glued2/food-caddy-stl/production/food_caddy_k1se_liner_hanger_plate.stl

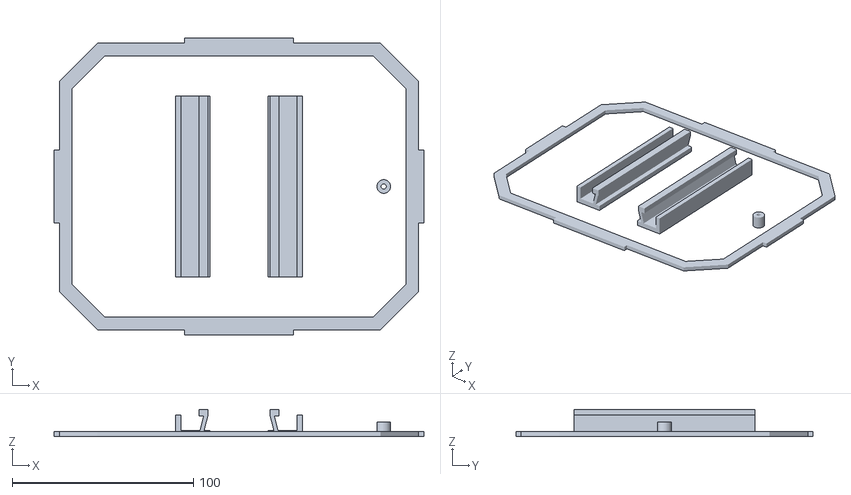
[picture p15: CAD file, 2026-09-11]
production/food_caddy_k1se_liner_hanger_plate.stl
204.0 x 164.0 x 15.0
