glued2/food-caddy-stl/spares/r4-coupon-rear-joint.stl

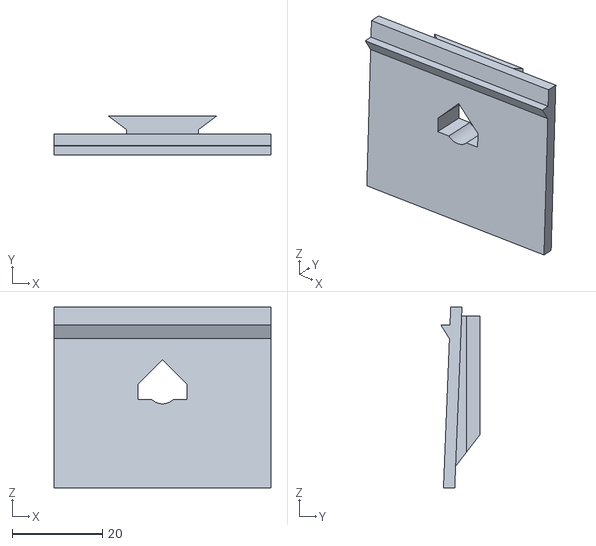
[picture p16: CAD file, 2026-09-12]
spares/r4-coupon-rear-joint.stl
48.0 x 8.66 x 40.0
