glued2/food-caddy-stl/spares/r4-coupon-gauge-keeper.stl

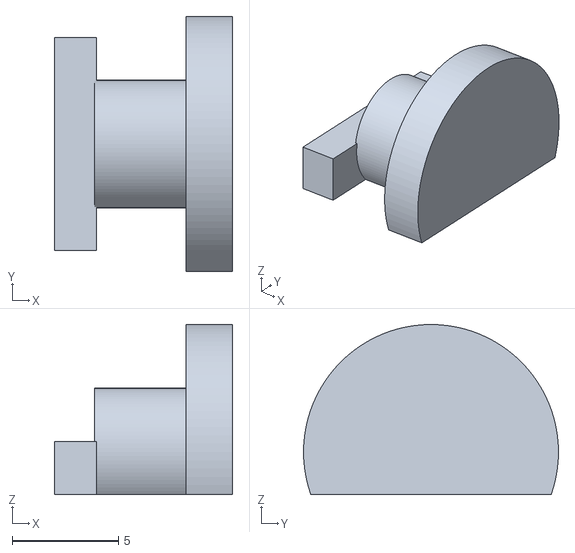
[picture p17: CAD file, 2026-09-12]
spares/r4-coupon-gauge-keeper.stl
8.40 x 12.0 x 8.00
