glued2/food-caddy-stl/production/food_caddy_k1se_failed_parts_only.stl

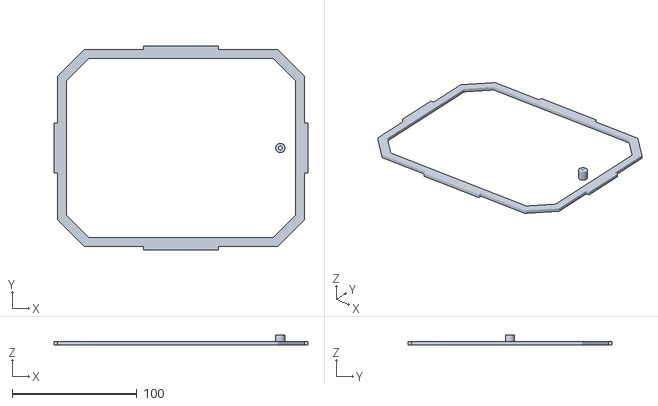
[picture p18: CAD file, 2026-09-11]
production/food_caddy_k1se_failed_parts_only.stl
204.0 x 164.0 x 8.00
