glued2/food-caddy-stl/spares/r4-coupon-corner.stl

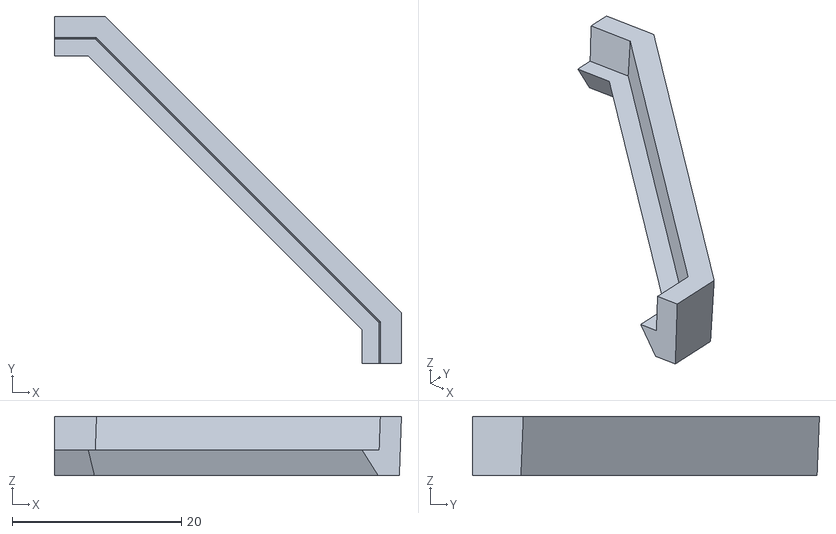
[picture p19: CAD file, 2026-09-12]
spares/r4-coupon-corner.stl
41.0 x 41.0 x 7.00
