glued2/food-caddy-stl/production/food_caddy_k1se_accessories_everything_bed_centered.stl

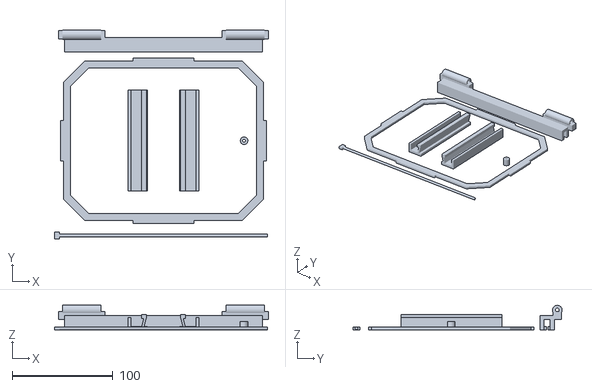
[picture p20: CAD file, 2026-09-11]
production/food_caddy_k1se_accessories_everything_bed_centered.stl
212.0 x 207.3 x 24.3
