glued2/food-caddy-stl/spares/r4-coupon-host-right.stl

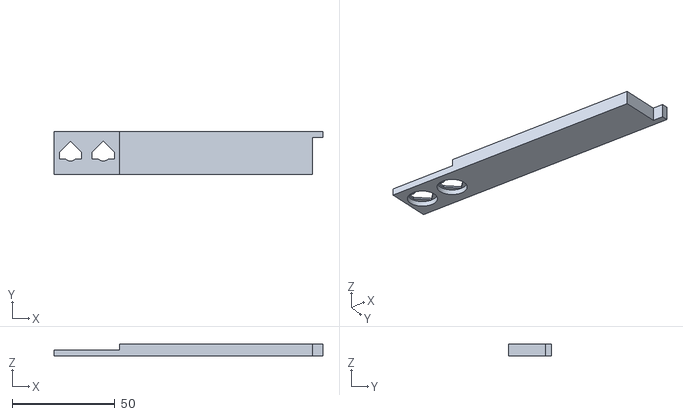
[picture p21: CAD file, 2026-09-12]
spares/r4-coupon-host-right.stl
131.0 x 21.0 x 6.00
