glued2/food-caddy-stl/spares/r4-coupon-axle-bores.stl

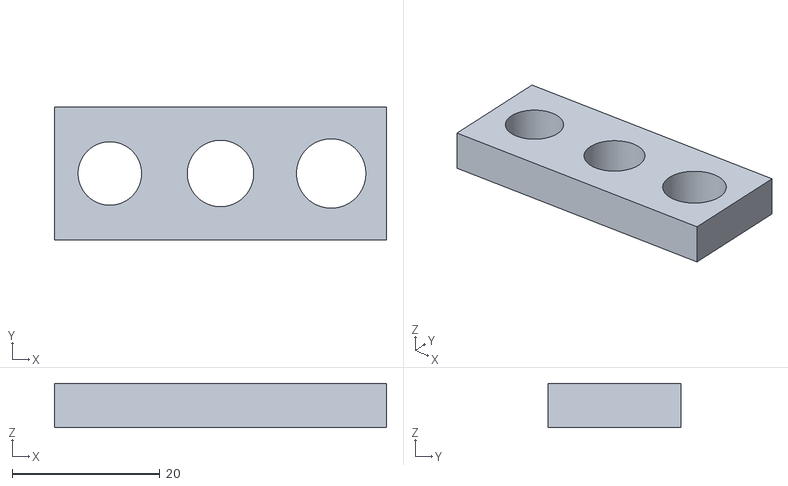
[picture p22: CAD file, 2026-09-12]
spares/r4-coupon-axle-bores.stl
45.0 x 18.0 x 6.00
