glued2/food-caddy-stl/spares/r4-coupon-lid-joint.stl

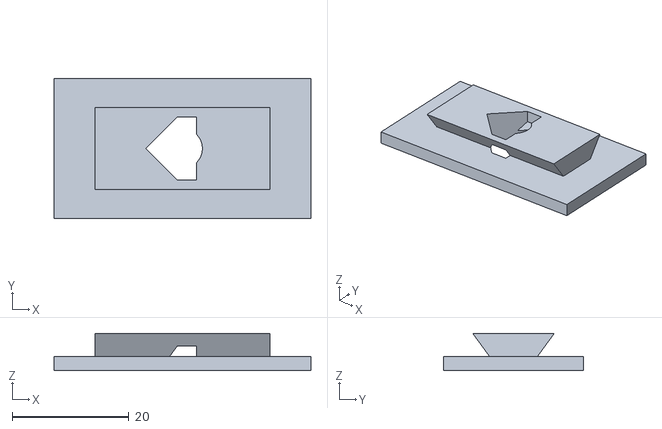
[picture p23: CAD file, 2026-09-12]
spares/r4-coupon-lid-joint.stl
44.0 x 24.0 x 6.40
