glued2/food-caddy-stl/production/food_caddy_k1se_hinge_kit_plate_bed_centered.stl

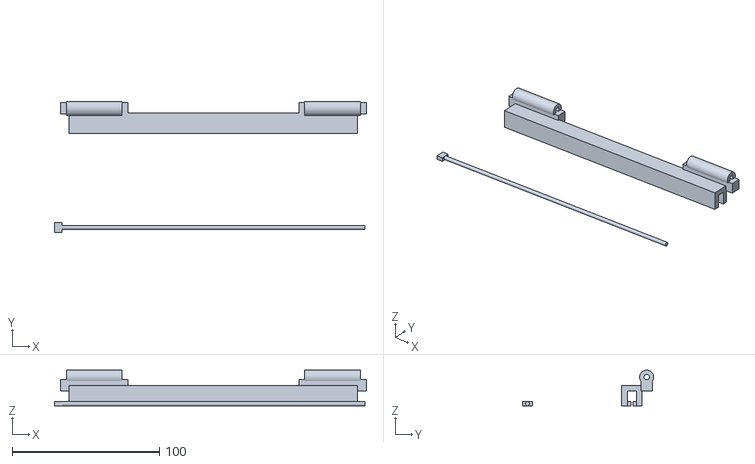
[picture p24: CAD file, 2026-09-07]
production/food_caddy_k1se_hinge_kit_plate_bed_centered.stl
212.0 x 89.3 x 24.3
