glued2/food-caddy-stl/spares/r4-hinge-rail.stl

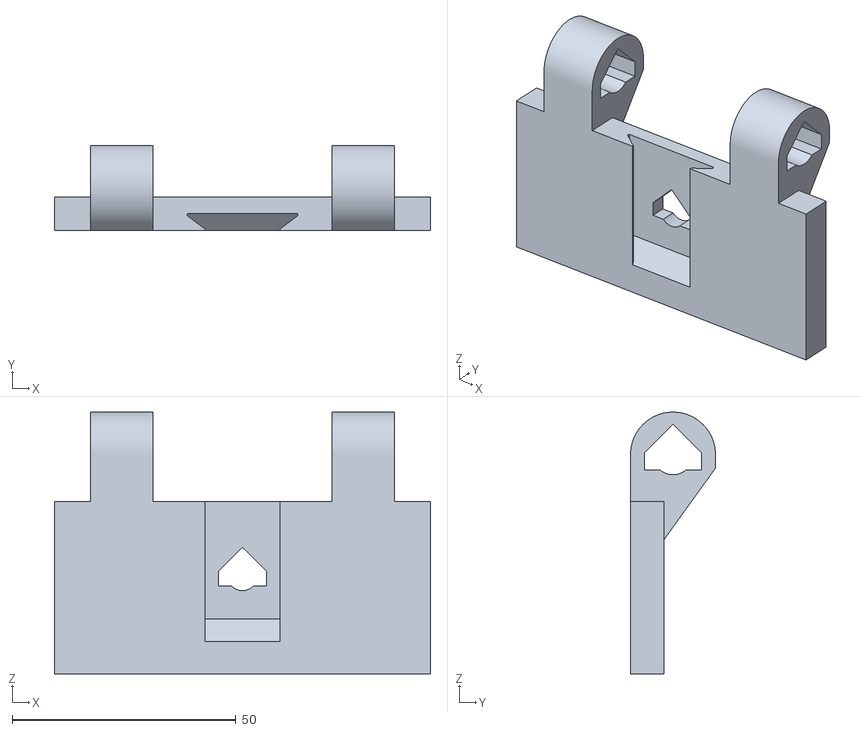
[picture p25: CAD file, 2026-09-12]
spares/r4-hinge-rail.stl
84.0 x 19.0 x 58.5
