glued2/food-caddy-stl/production/food_caddy_k1se_body_216mm_bed_centered.stl

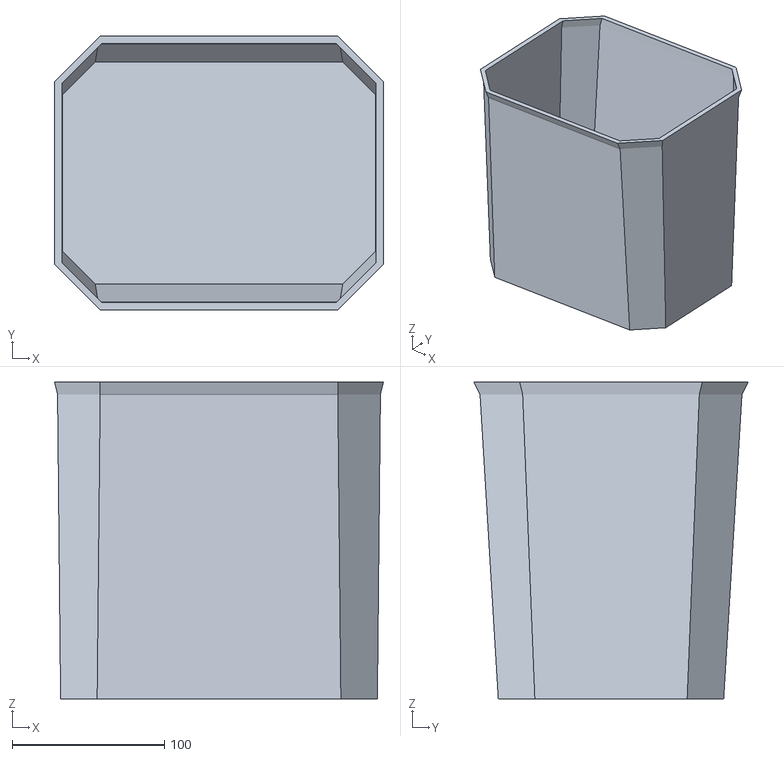
[picture p26: CAD file, 2026-09-07]
production/food_caddy_k1se_body_216mm_bed_centered.stl
216.0 x 180.0 x 208.0
