glued2/food-caddy-stl/spares/r4-rear-gate-keeper.stl

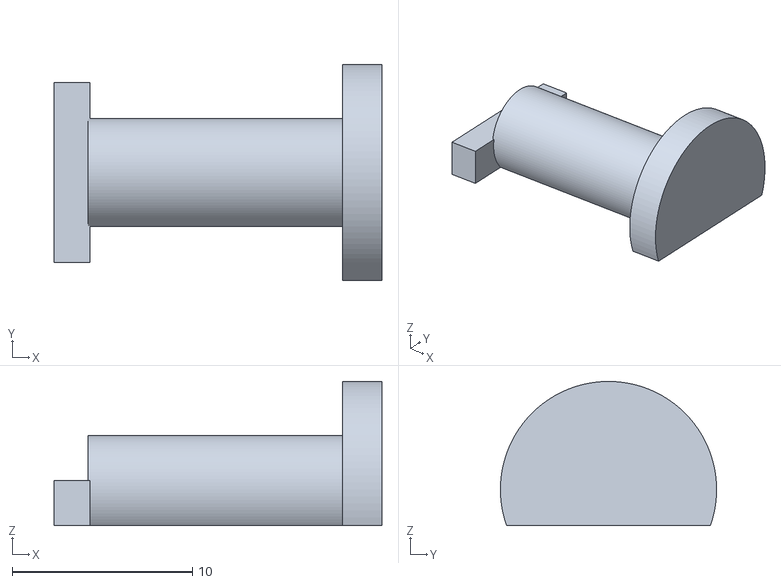
[picture p27: CAD file, 2026-09-12]
spares/r4-rear-gate-keeper.stl
18.2 x 12.0 x 8.00
