glued2/food-caddy-stl/spares/food_caddy_k1se_hinge_retainer_collar_spare.stl

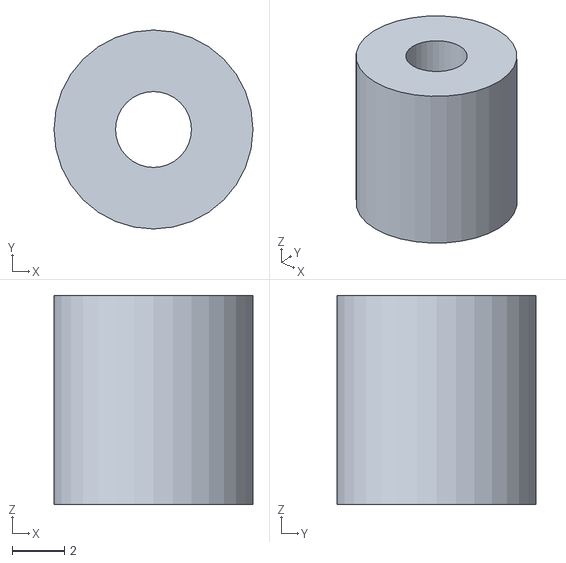
[picture p28: CAD file, 2026-09-11]
spares/food_caddy_k1se_hinge_retainer_collar_spare.stl
7.60 x 7.60 x 8.00
