glued2/food-caddy-stl/spares/food_caddy_k1se_bag_retainer_ring_spare.stl

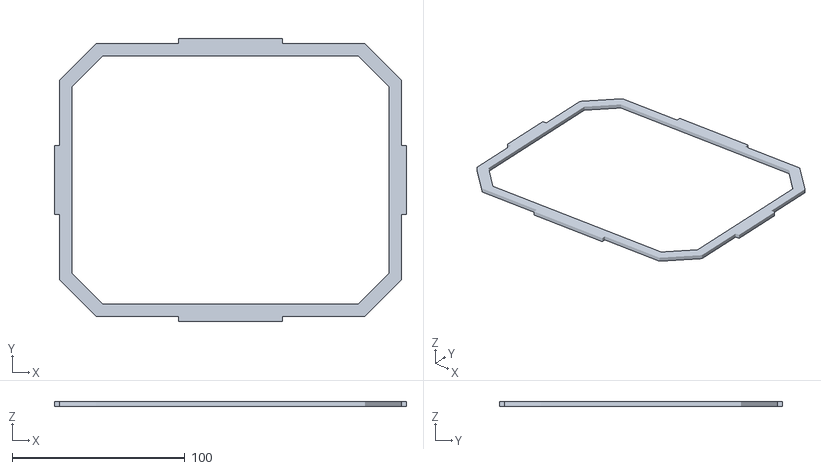
[picture p29: CAD file, 2026-09-11]
spares/food_caddy_k1se_bag_retainer_ring_spare.stl
204.0 x 164.0 x 2.80
