glued2/food-caddy-stl/spares/food_caddy_k1se_hinge_pin_spare.stl

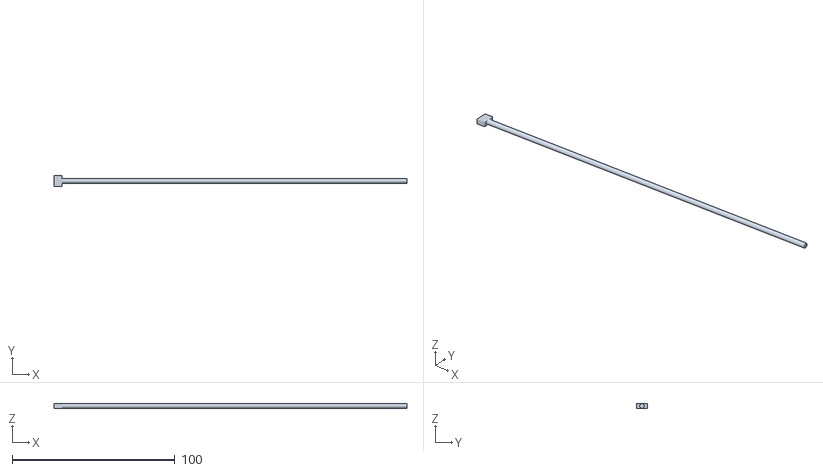
[picture p30: CAD file, 2026-09-07]
spares/food_caddy_k1se_hinge_pin_spare.stl
217.0 x 7.00 x 2.90
